rusaakkmods/modulogue_vco/docs/reviews/04_pulse_wave.png

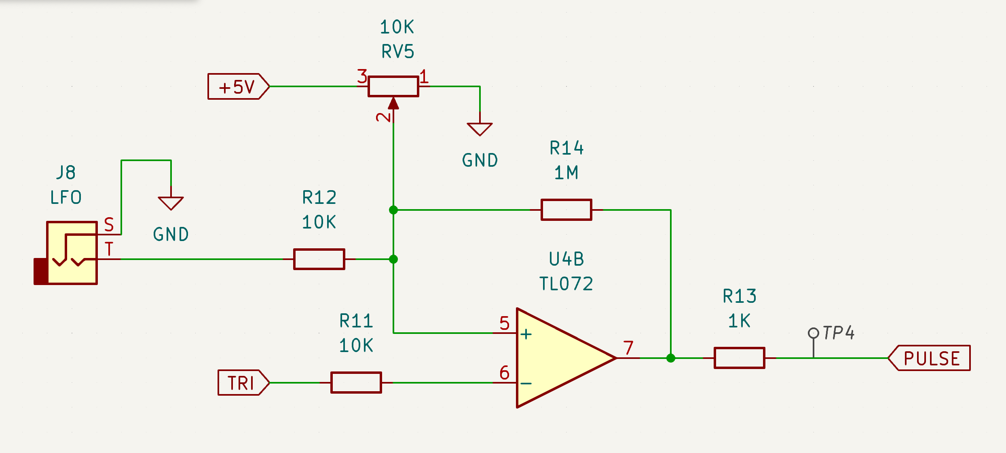
docs/reviews/04_pulse_wave.png
