rusaakkmods/modulogue_vco/docs/reviews/05_noise_generator_v2.png

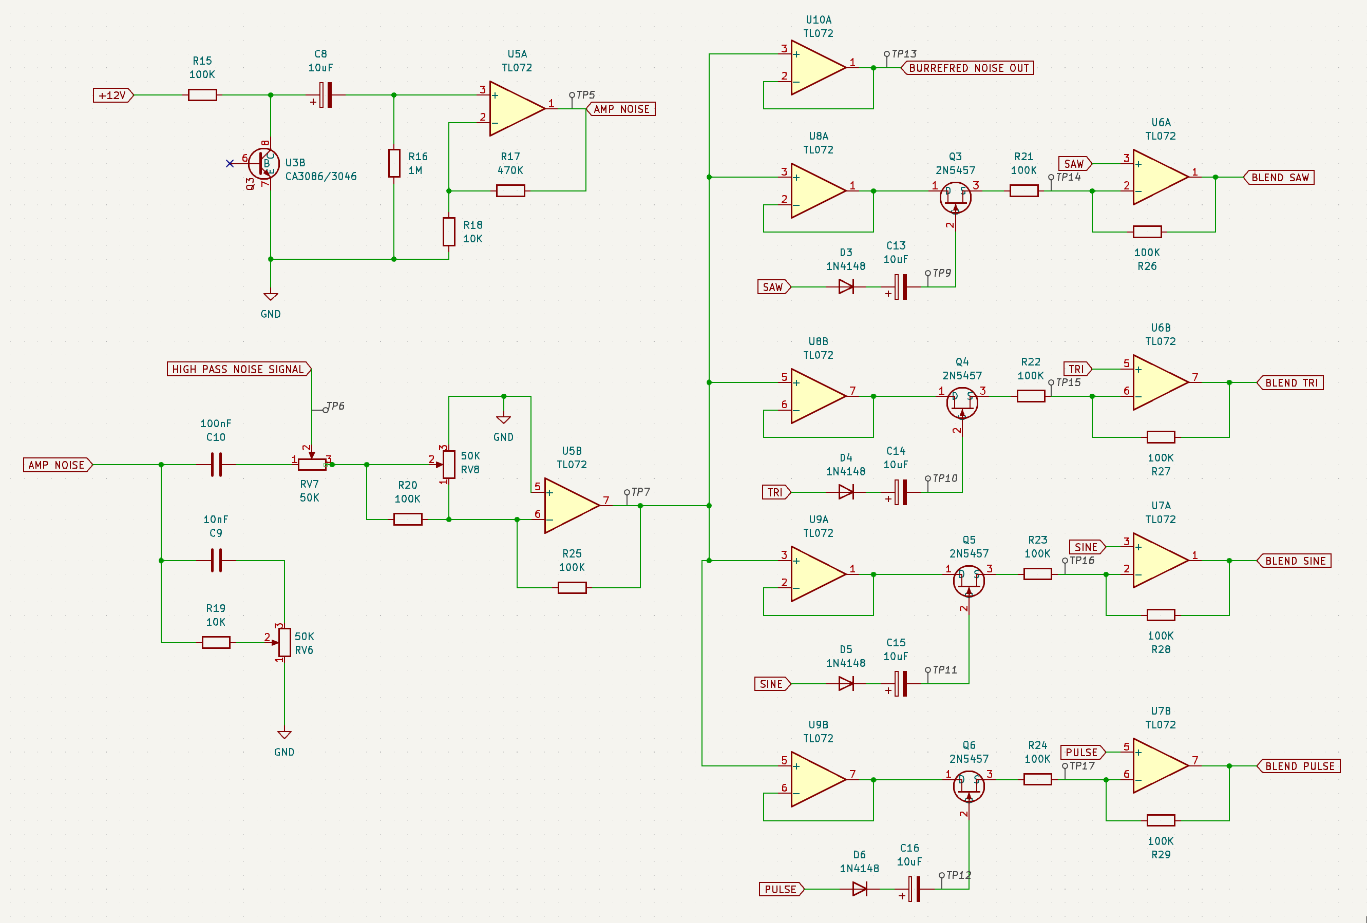
docs/reviews/05_noise_generator_v2.png
