rusaakkmods/modulogue_vco/docs/reviews/07_power_connector.png

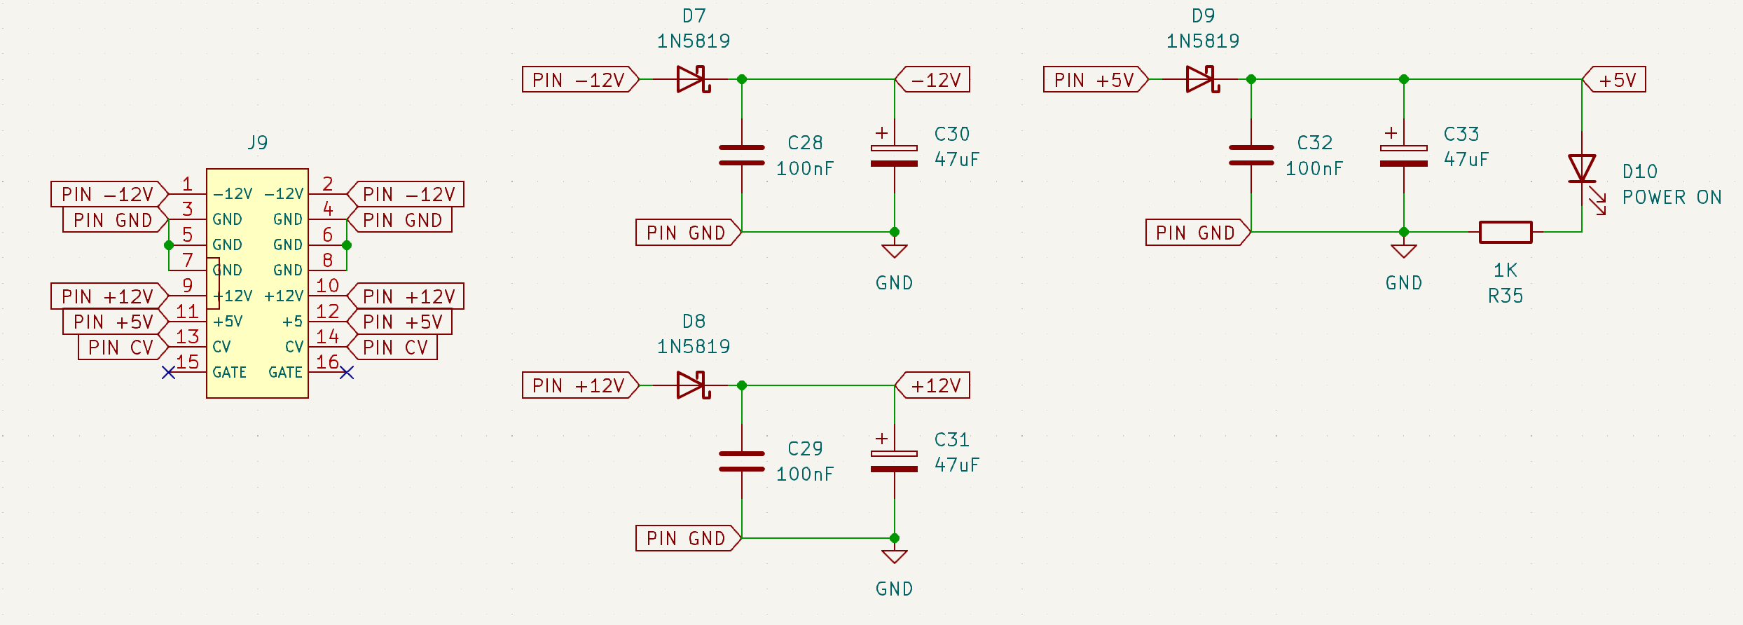
docs/reviews/07_power_connector.png
